nathanfu88/opentdcs/kicad/power.kicad_sch

## KiCad design kicad/power.kicad_sch (2026-02-19)

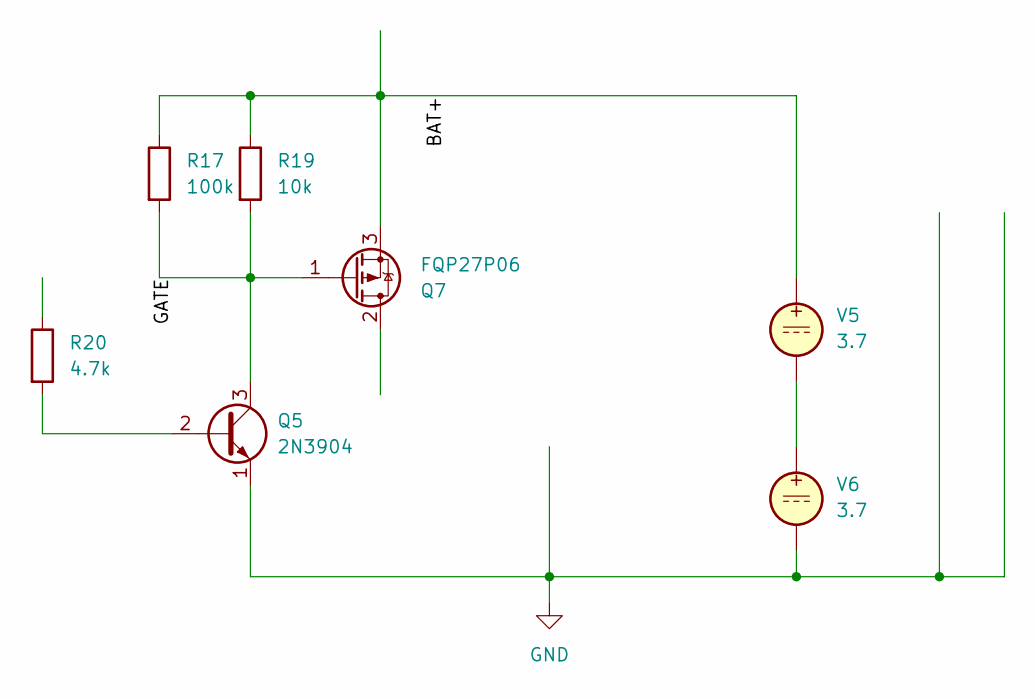
[picture p7: schematic power.kicad_sch]

Parts:
Q5: 2N3904; TO-92_Inline
Q7: FQP27P06; TO-220-3_Vertical
R17: 100k
R19: 10k
R20: 4.7k
V5, V6: 3.7

Connections:
BAT+: Q7.3 (S), R17.1, R19.1, V5.1
GATE: Q5.3 (C), Q7.1 (G), R17.2, R19.2
GND: Q5.1 (E), V6.2
unnamed: Q5.2 (B), R20.2
unnamed: V5.2, V6.1
